JSmith01/zx-keyboard/delta/delta-c keyboard.jpg

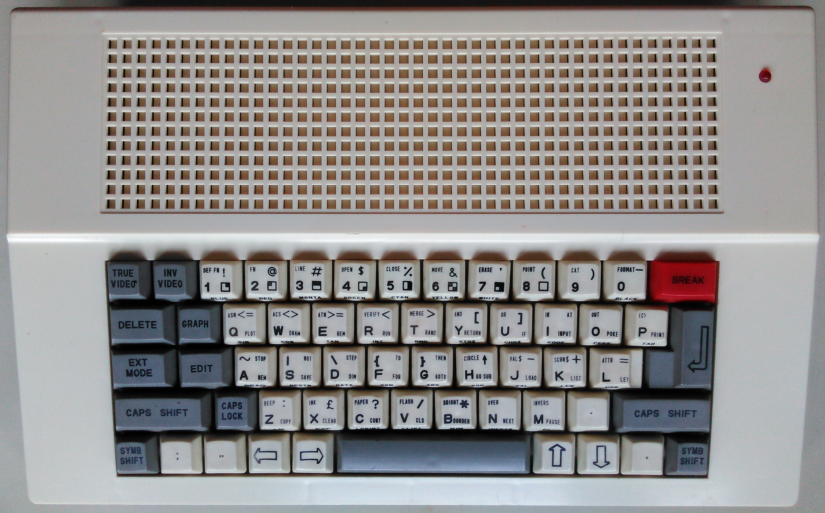
delta/delta-c keyboard.jpg
