JSmith01/zx-keyboard/keycap blueprints/key 1-1.jpg

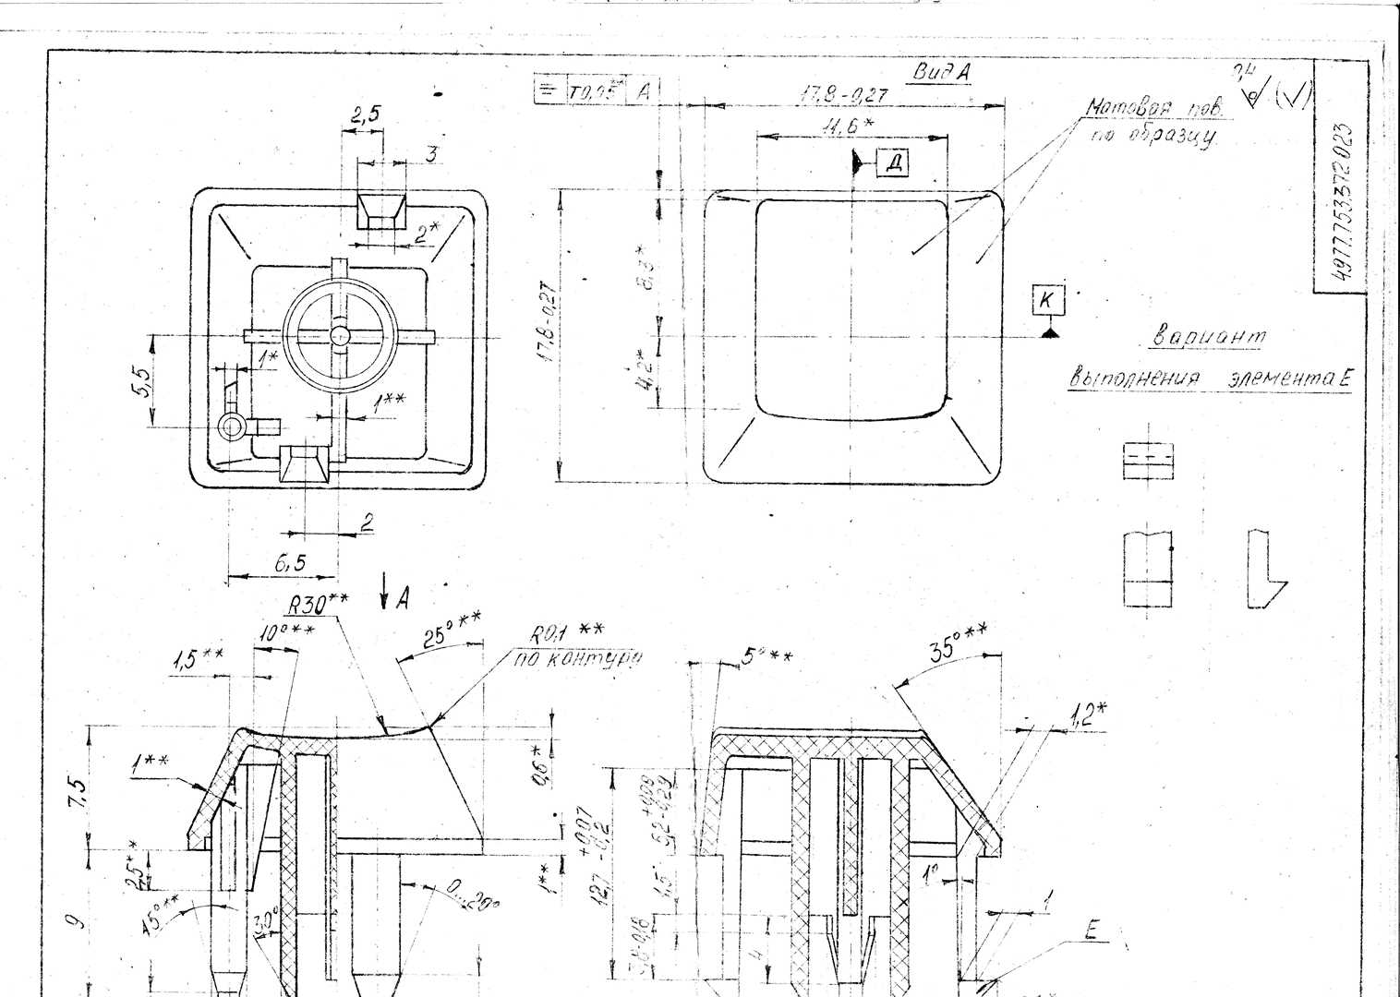
keycap blueprints/key 1-1.jpg
