JSmith01/zx-keyboard/keycap blueprints/key 2-1.jpg

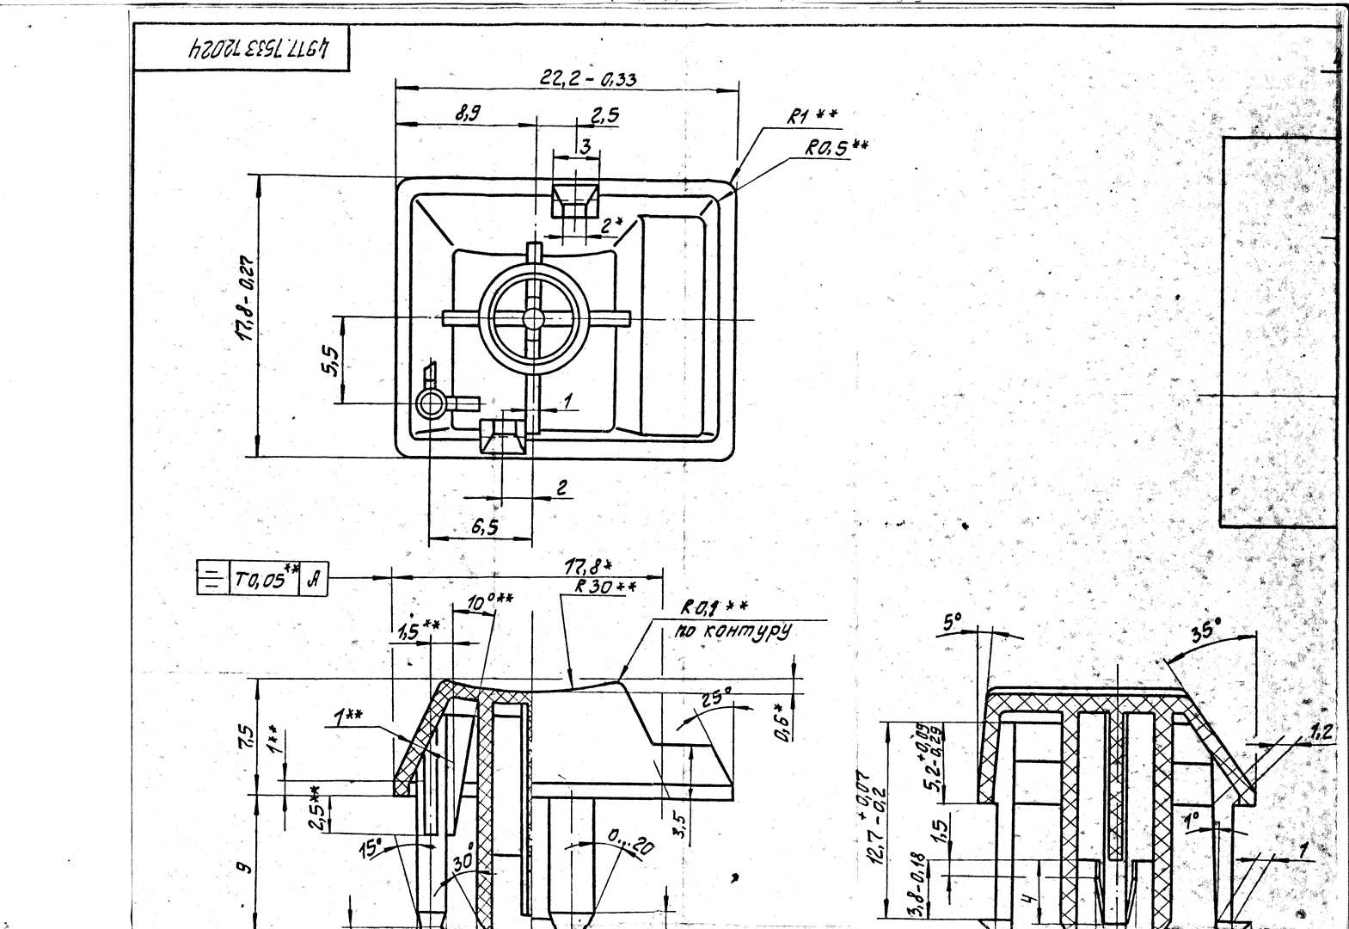
keycap blueprints/key 2-1.jpg
