JSmith01/zx-keyboard/keycap blueprints/key 2-2.jpg

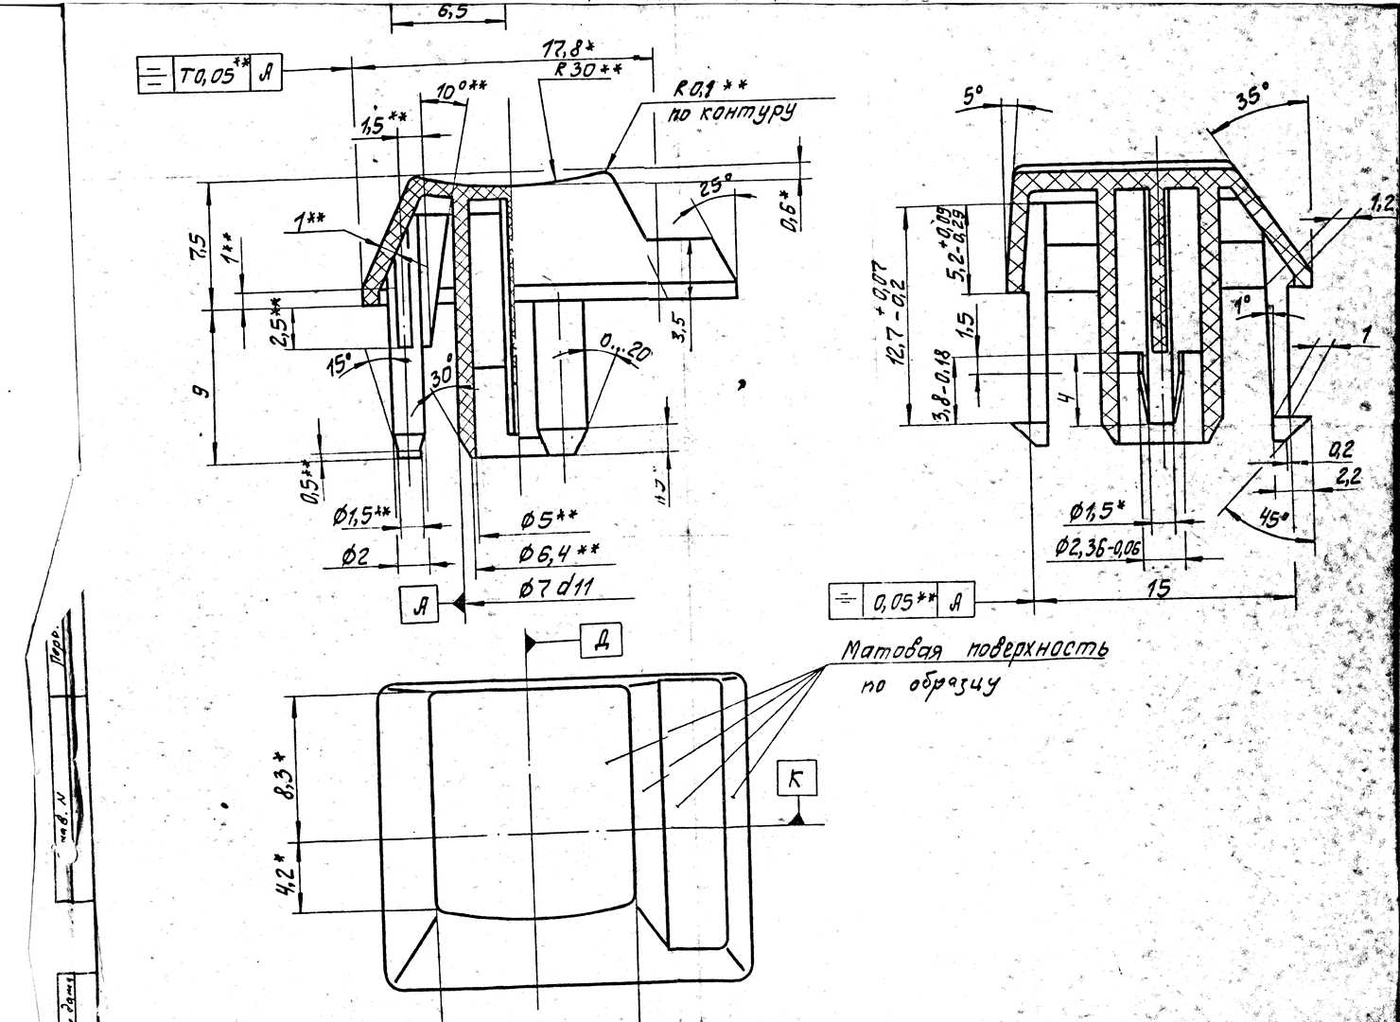
keycap blueprints/key 2-2.jpg
