JSmith01/zx-keyboard/keycap blueprints/key 2-3.jpg

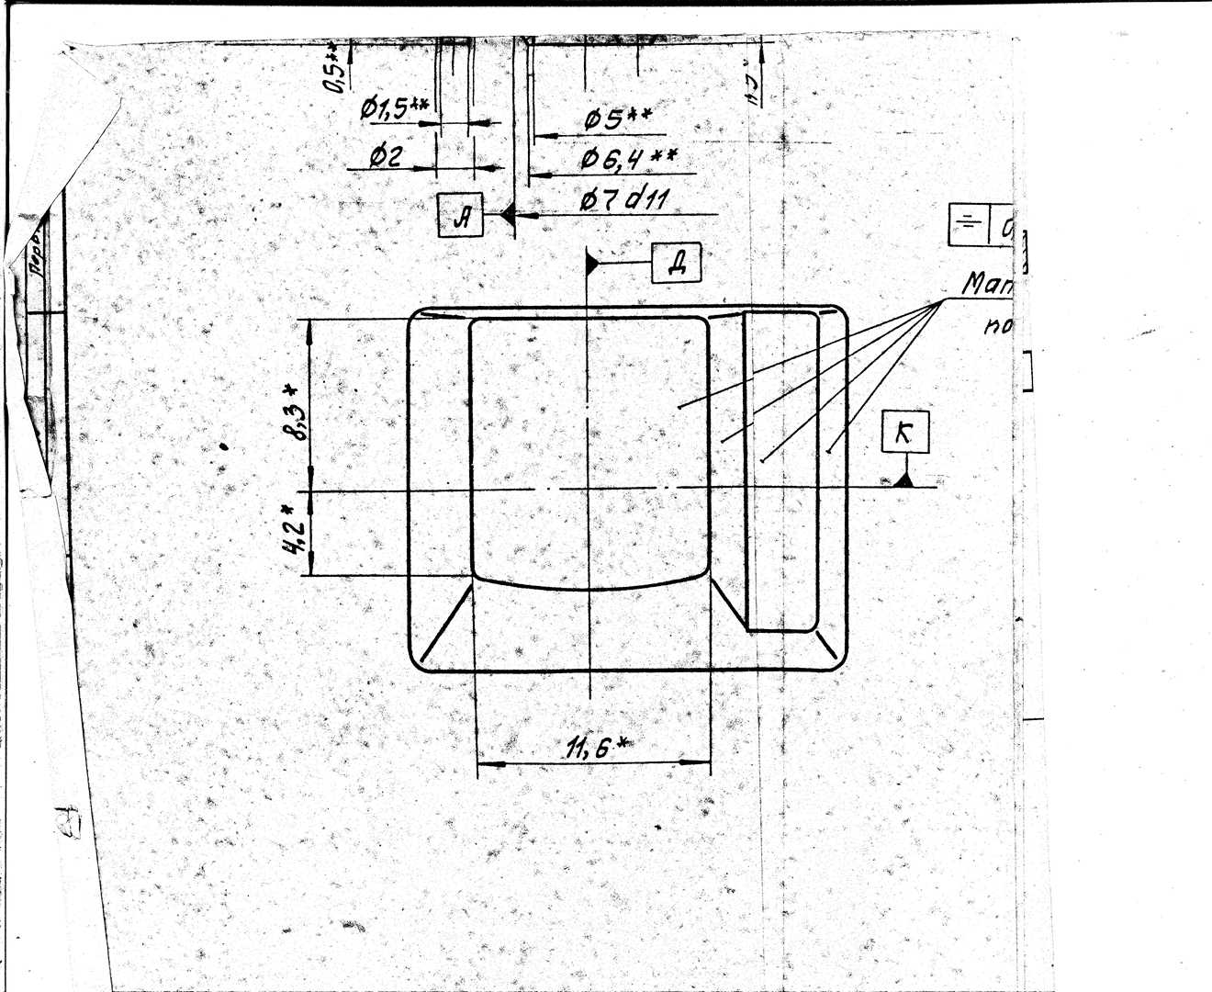
keycap blueprints/key 2-3.jpg
