JSmith01/zx-keyboard/keycap blueprints/key 3-1.jpg

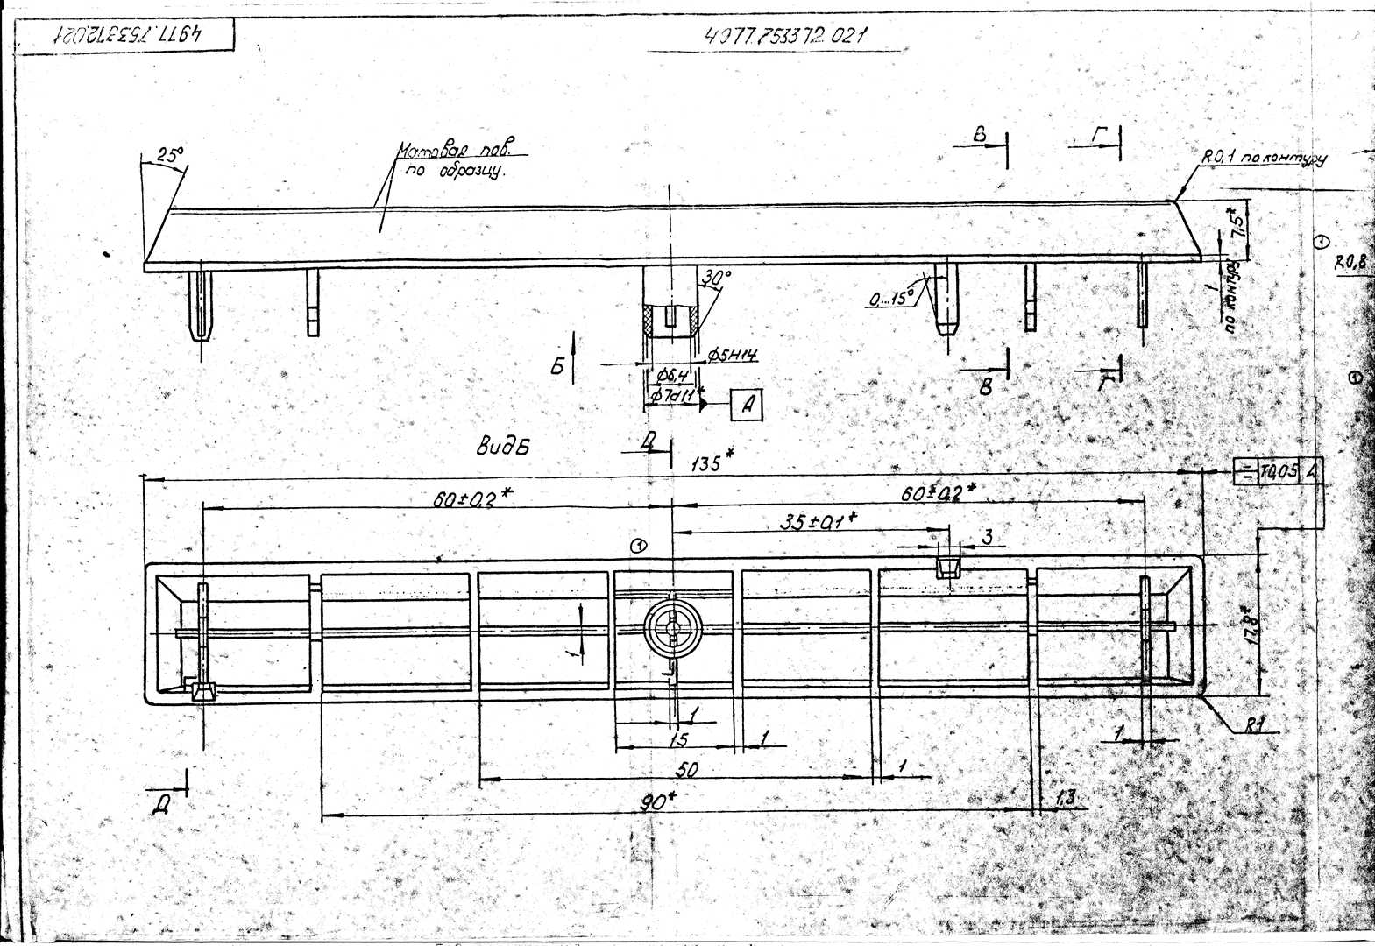
keycap blueprints/key 3-1.jpg
