JSmith01/zx-keyboard/keycap blueprints/key 3-2.jpg

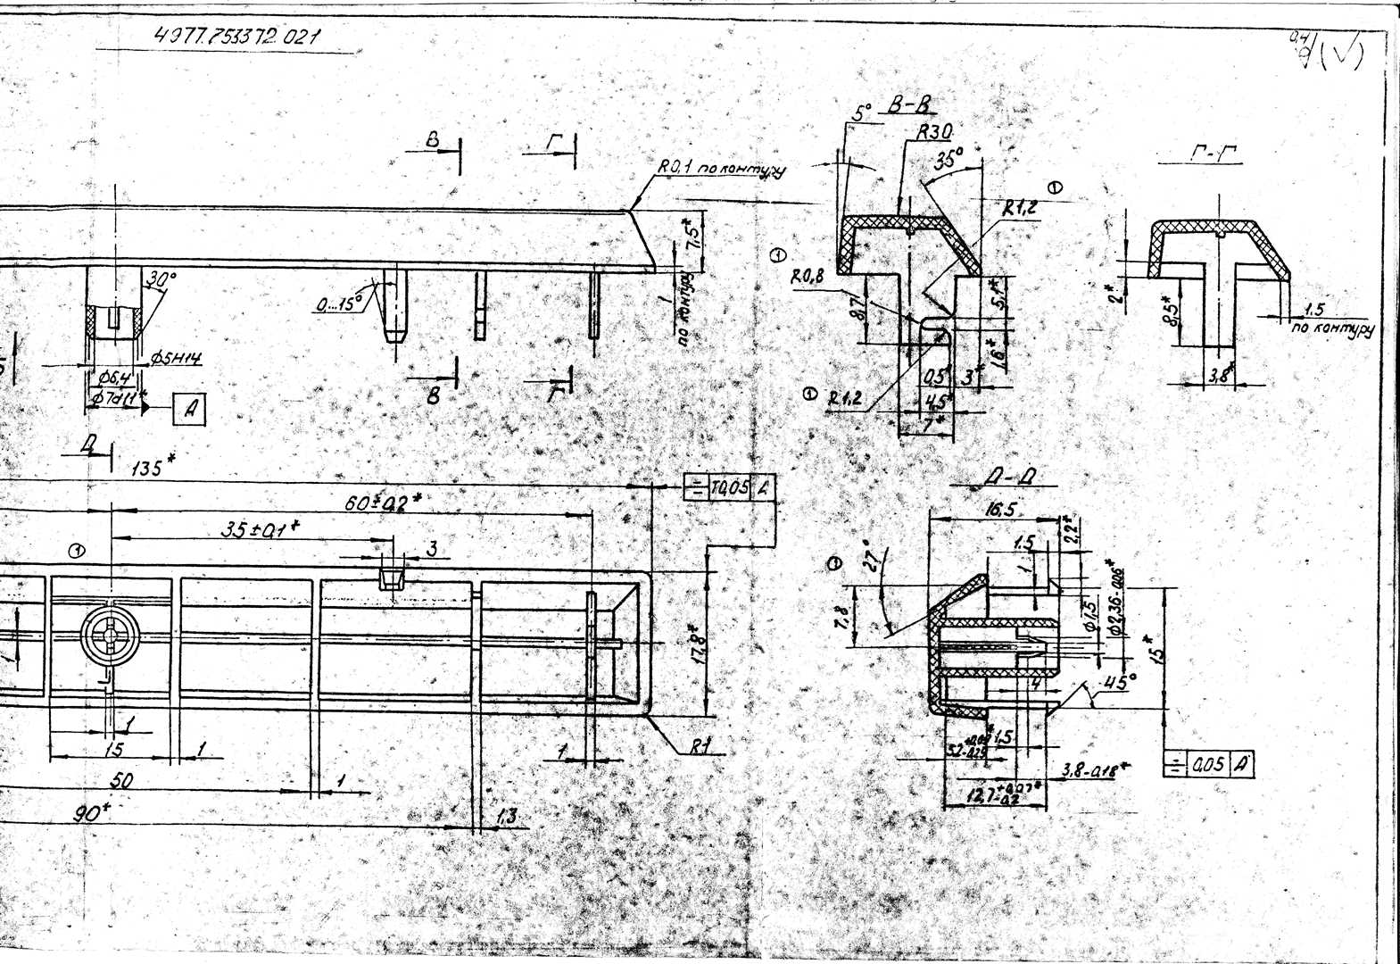
keycap blueprints/key 3-2.jpg
