JSmith01/zx-keyboard/keycap blueprints/key 4-1.jpg

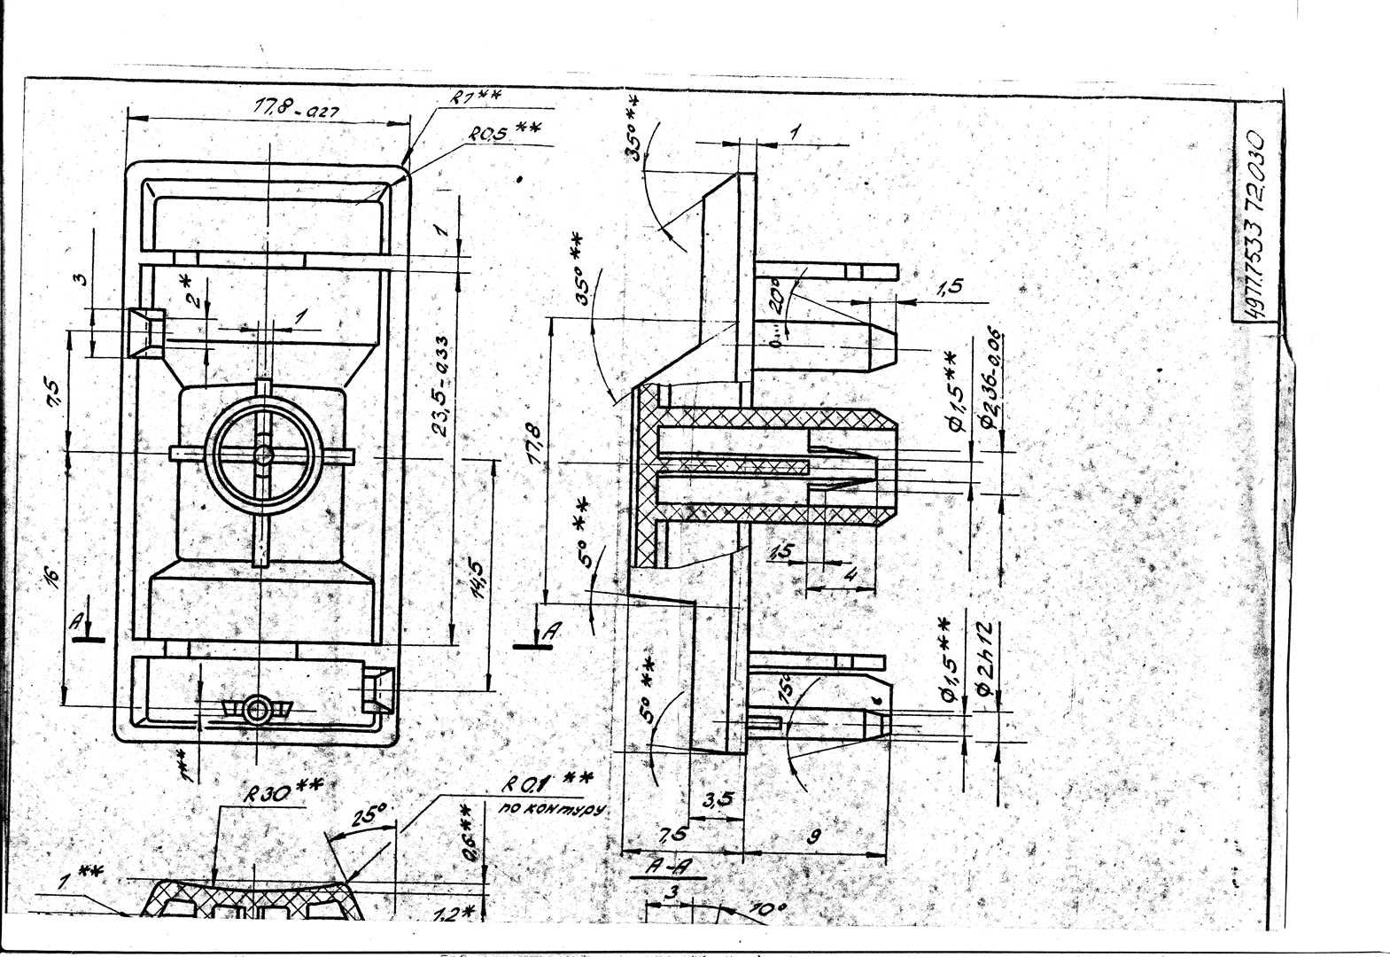
keycap blueprints/key 4-1.jpg
