JSmith01/zx-keyboard/keycap blueprints/key 4-2.jpg

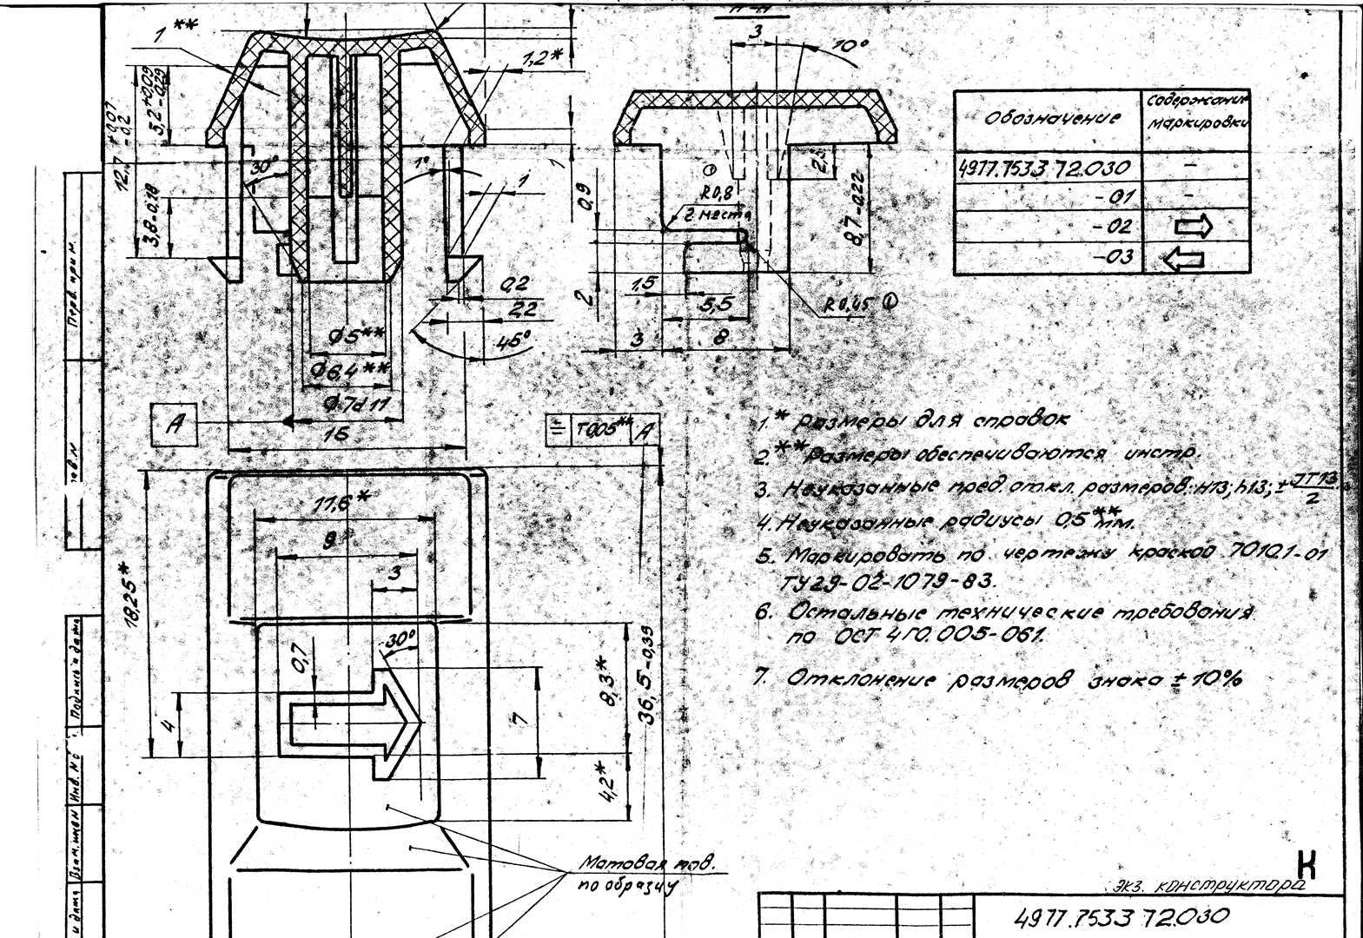
keycap blueprints/key 4-2.jpg
