JSmith01/zx-keyboard/keycap blueprints/key 4-3.jpg

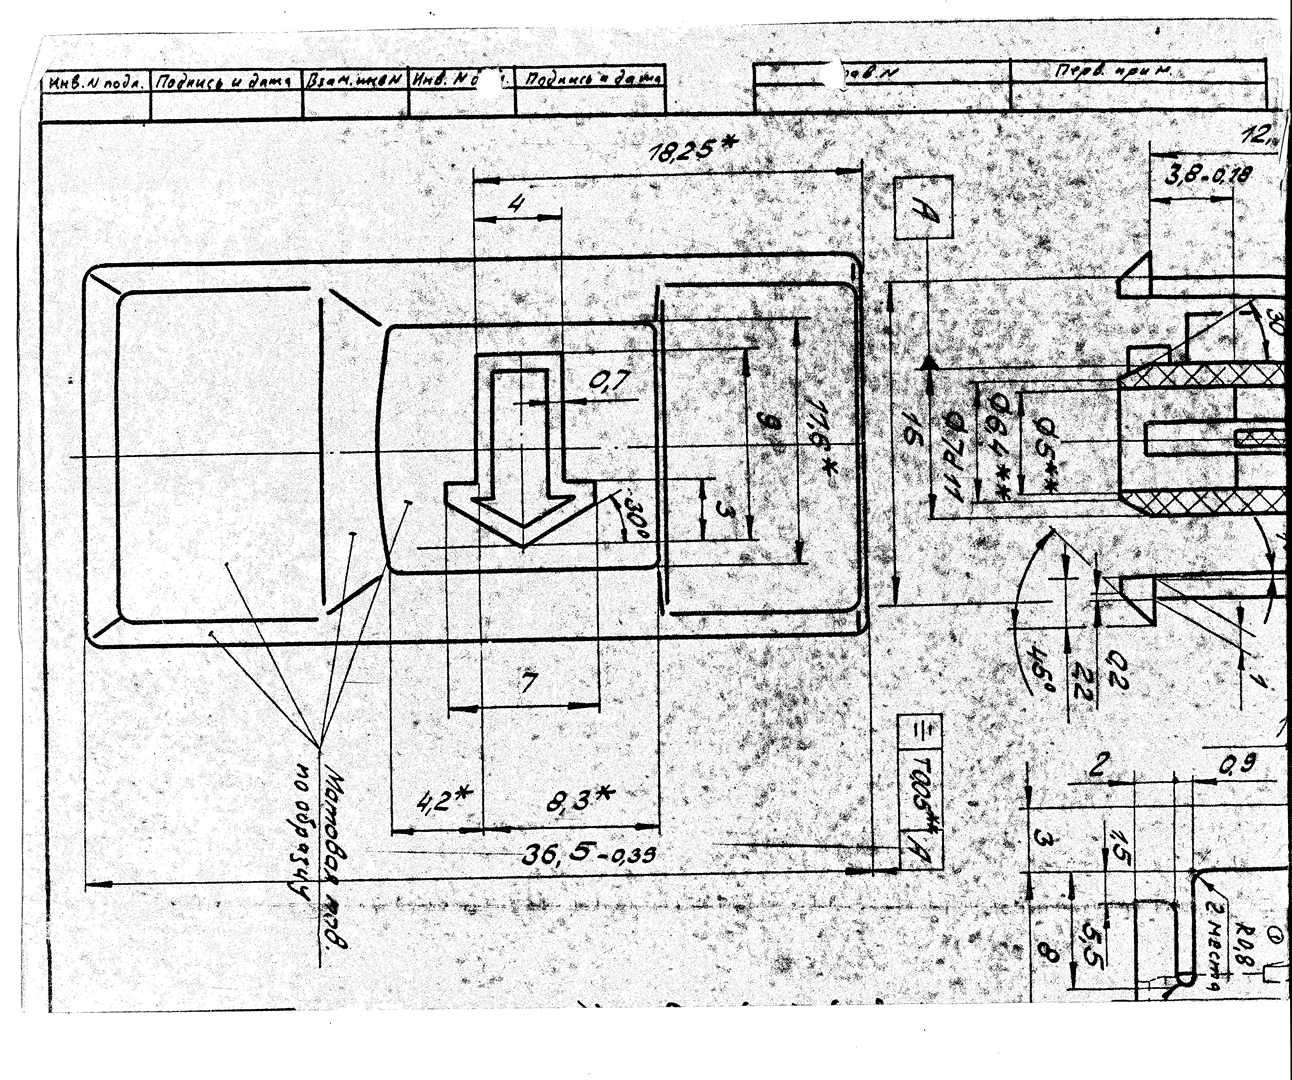
keycap blueprints/key 4-3.jpg
