JSmith01/zx-keyboard/keycap blueprints/key 5-2.jpg

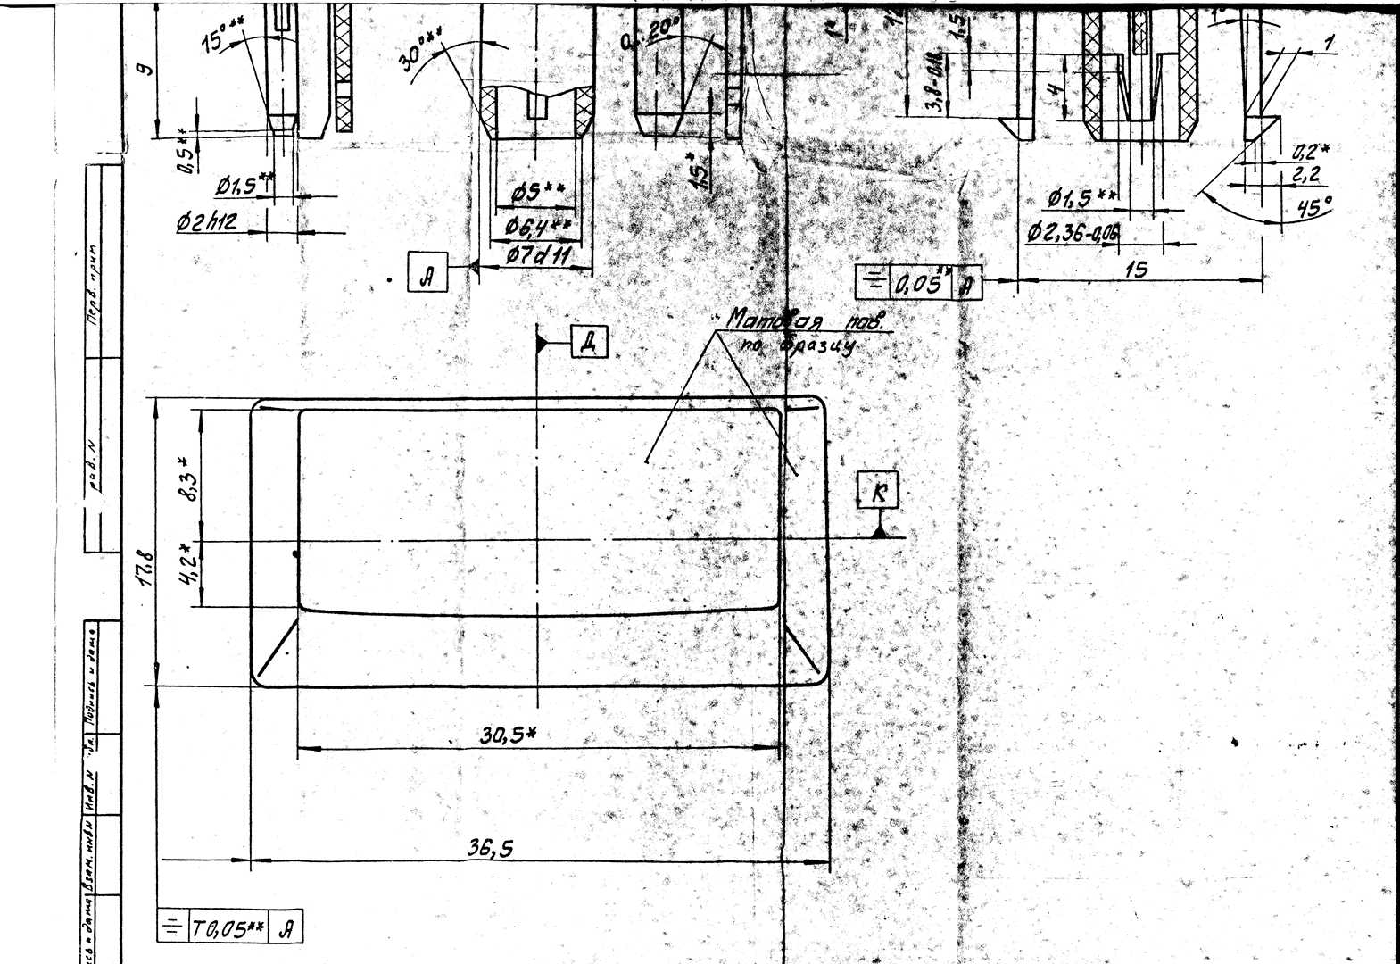
keycap blueprints/key 5-2.jpg
