JSmith01/zx-keyboard/keycap blueprints/key 6-2.jpg

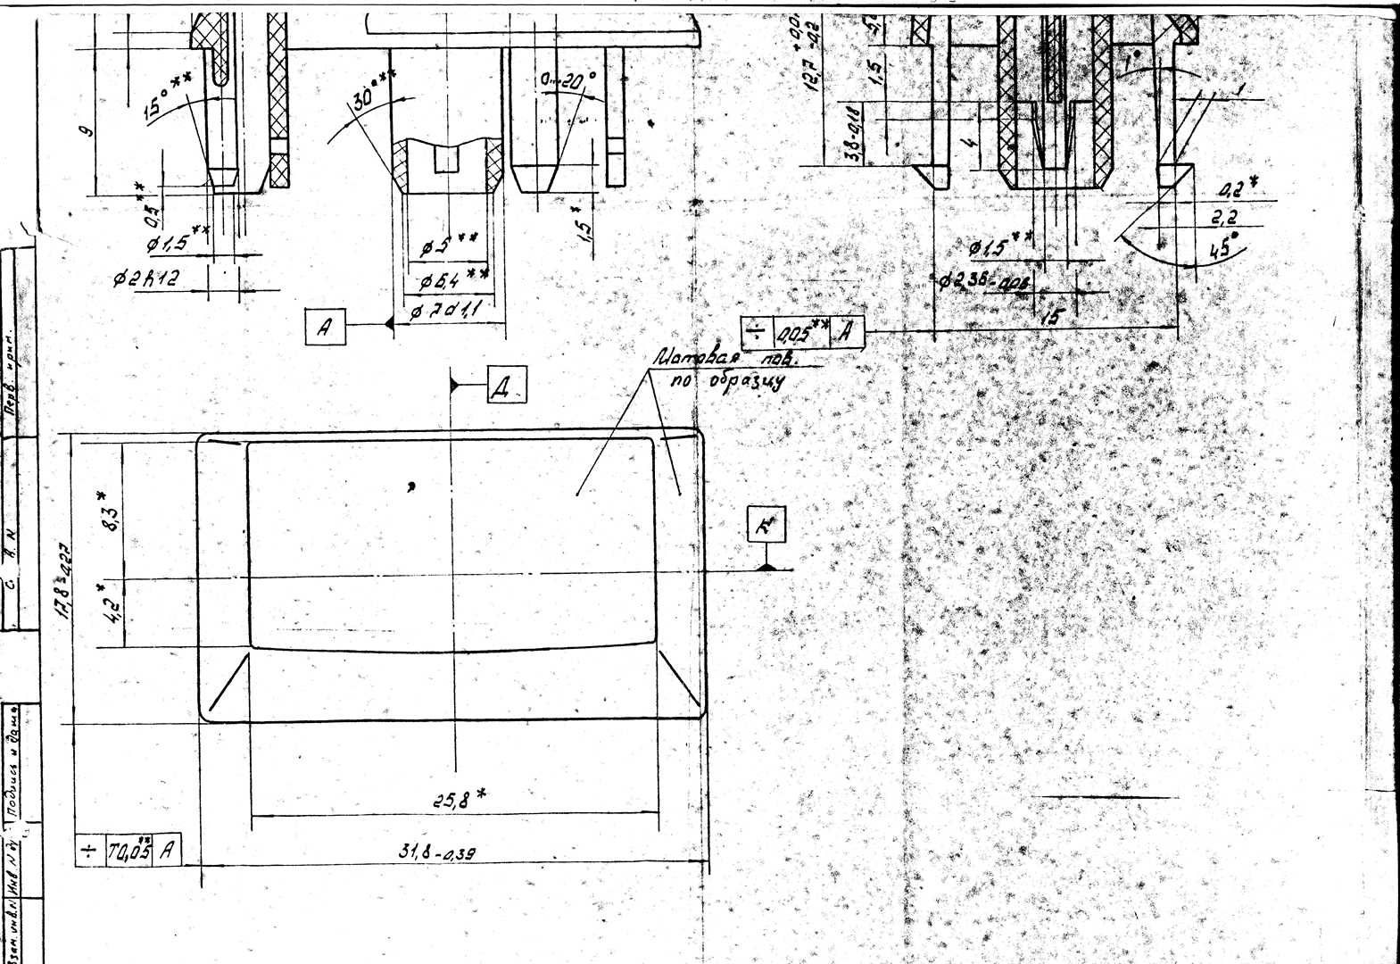
keycap blueprints/key 6-2.jpg
