JSmith01/zx-keyboard/keycap blueprints/key 7-1.jpg

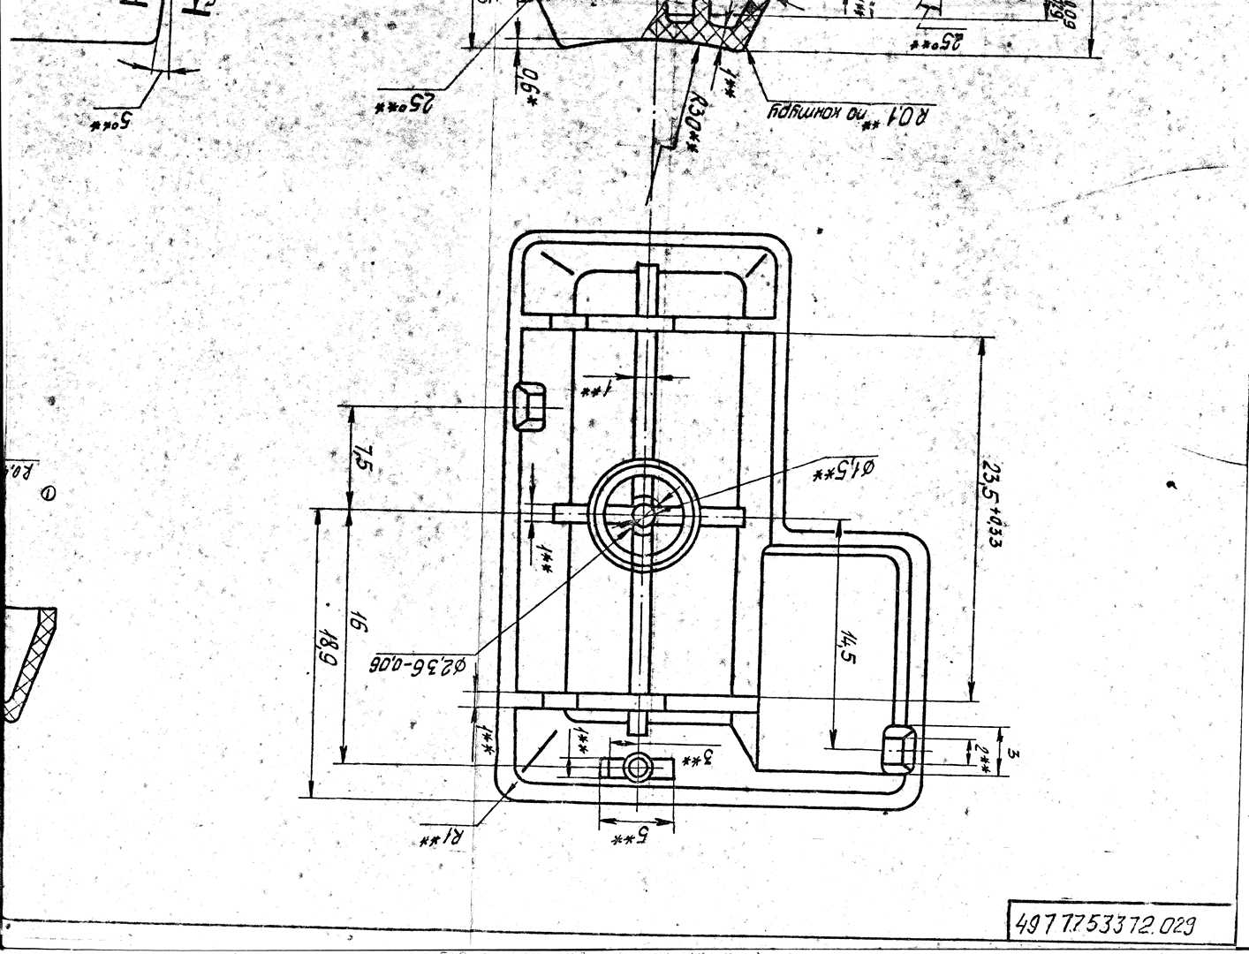
keycap blueprints/key 7-1.jpg
