JSmith01/zx-keyboard/keycap blueprints/key 7-2.jpg

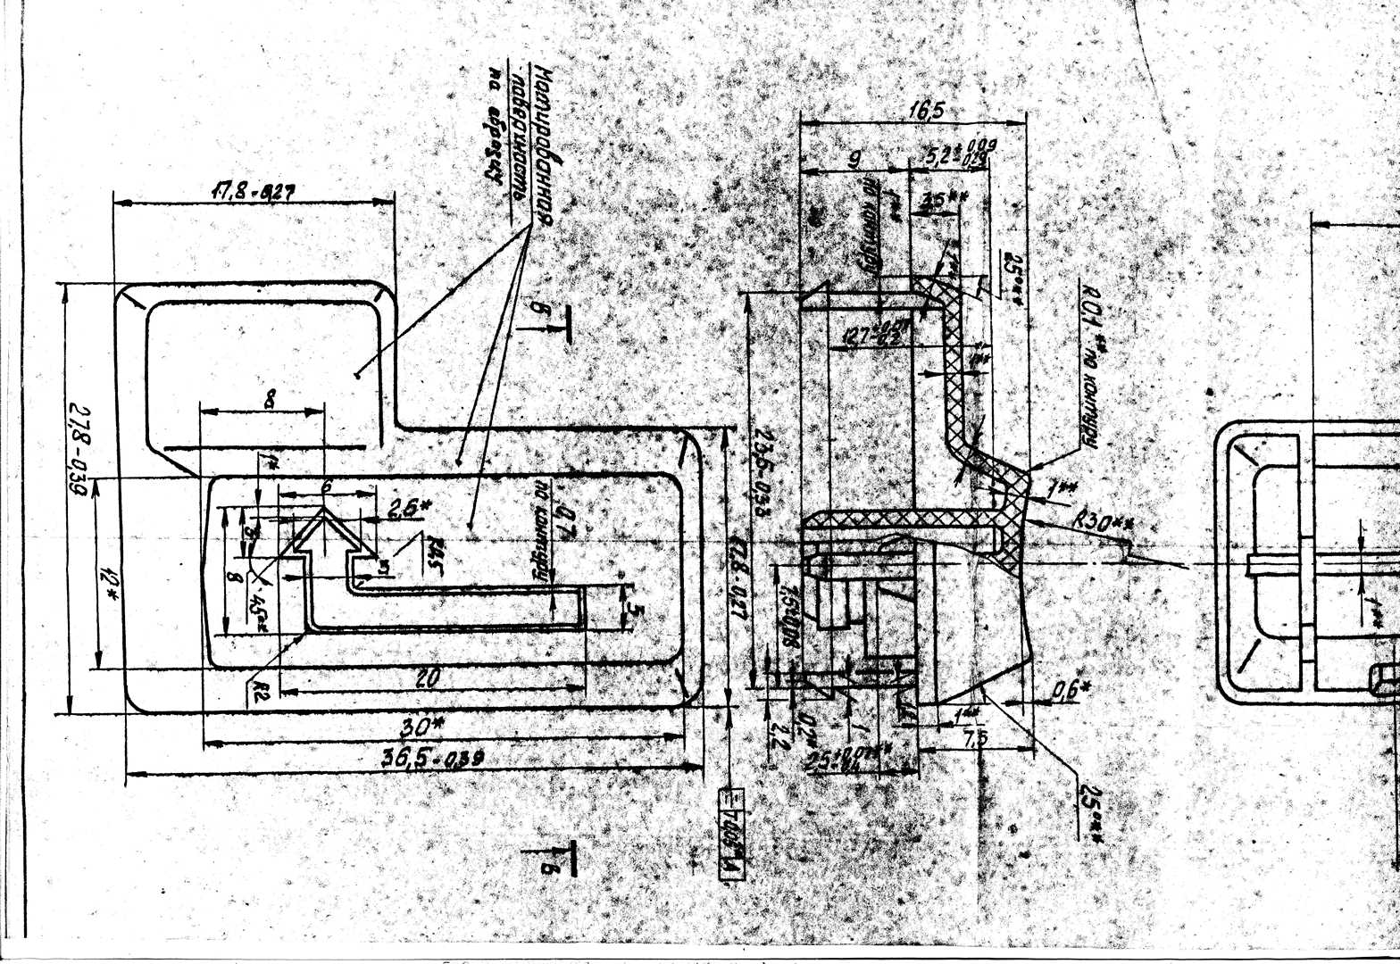
keycap blueprints/key 7-2.jpg
