JSmith01/zx-keyboard/keycap blueprints/key 7-3.jpg

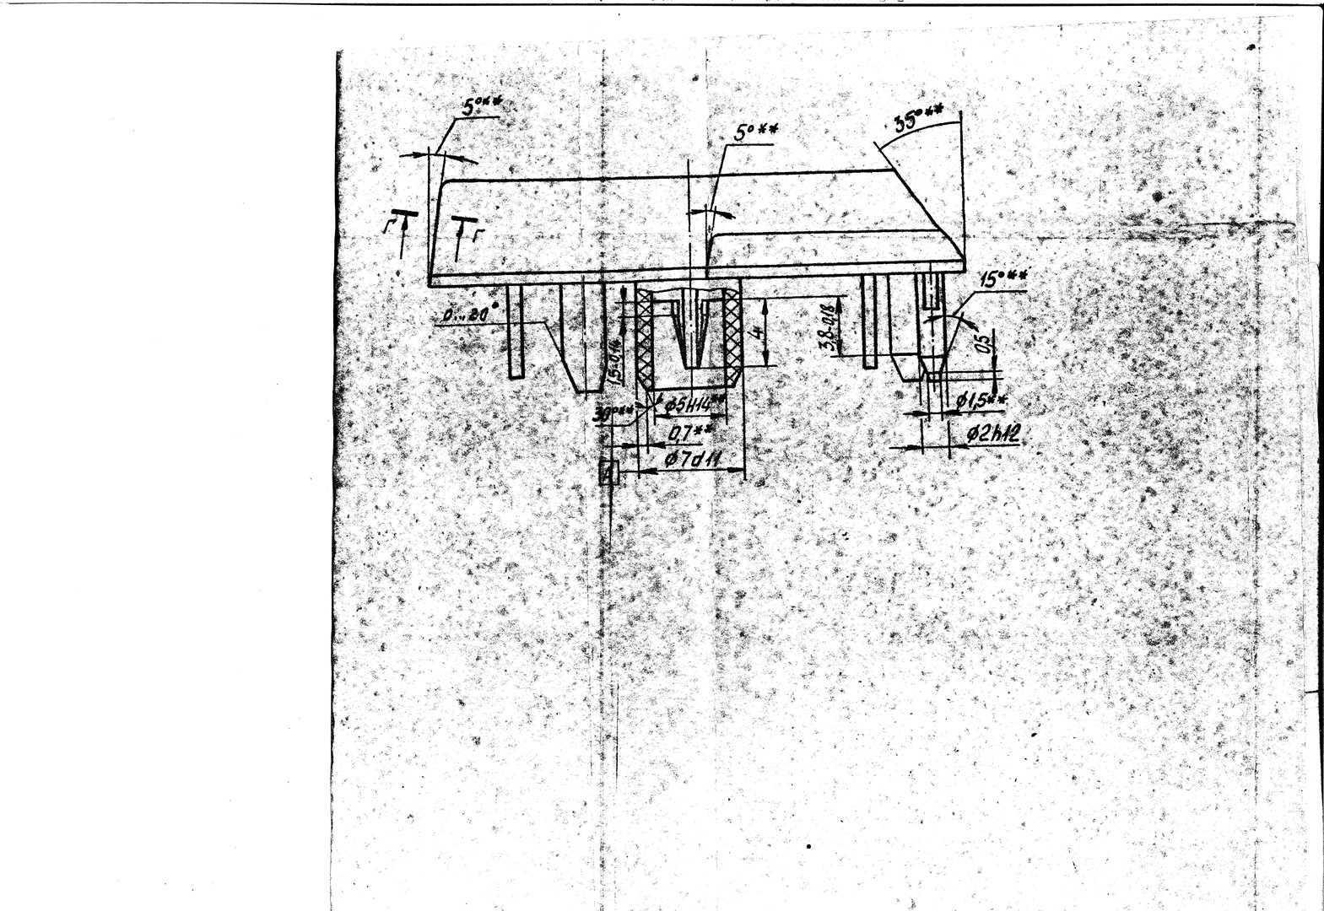
keycap blueprints/key 7-3.jpg
