JSmith01/zx-keyboard/keycap blueprints/key 7-4.jpg

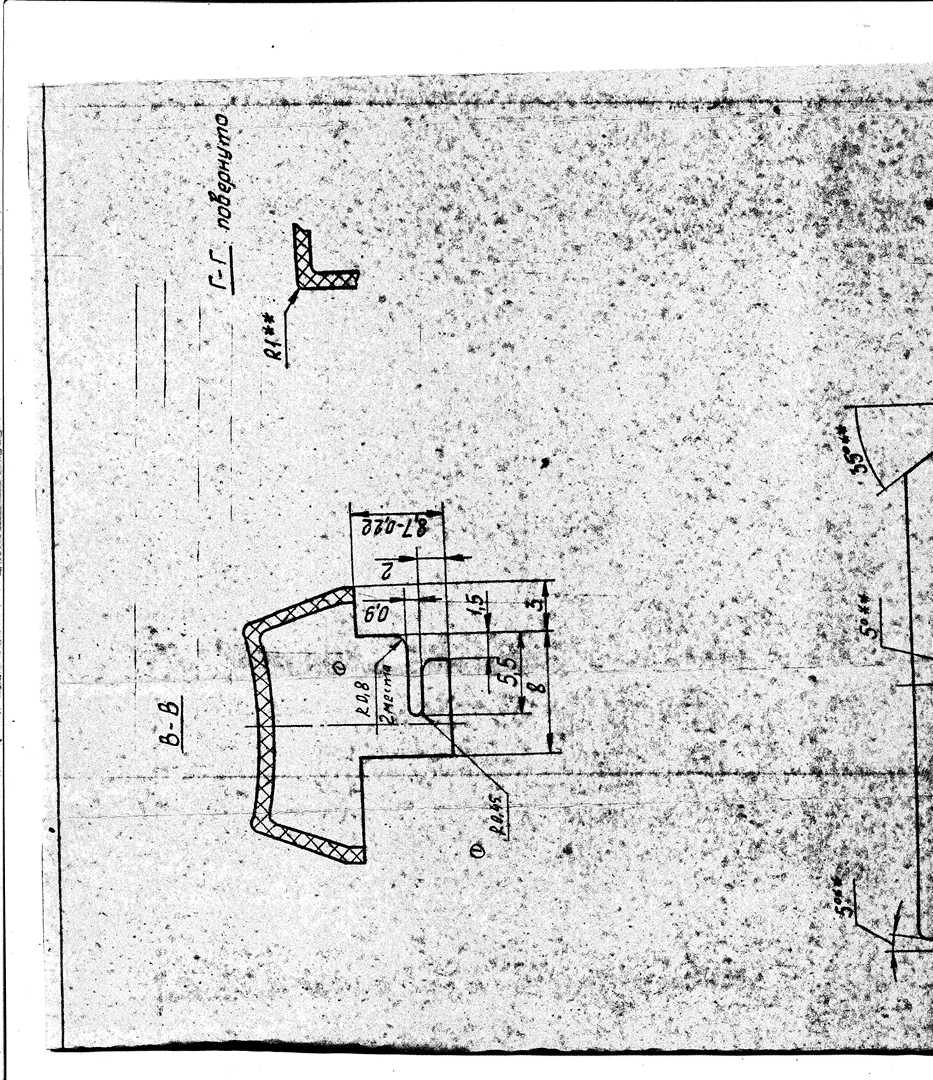
keycap blueprints/key 7-4.jpg
