JSmith01/zx-keyboard/pc-58-case/pictures/Image00006.jpg

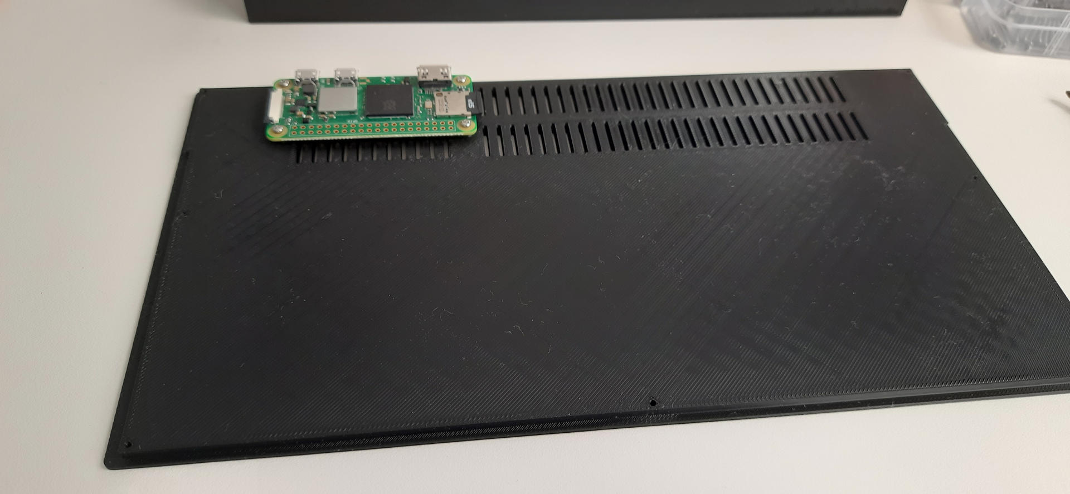
pc-58-case/pictures/Image00006.jpg
