JSmith01/zx-keyboard/pc-58-case/pictures/Image00007.jpg

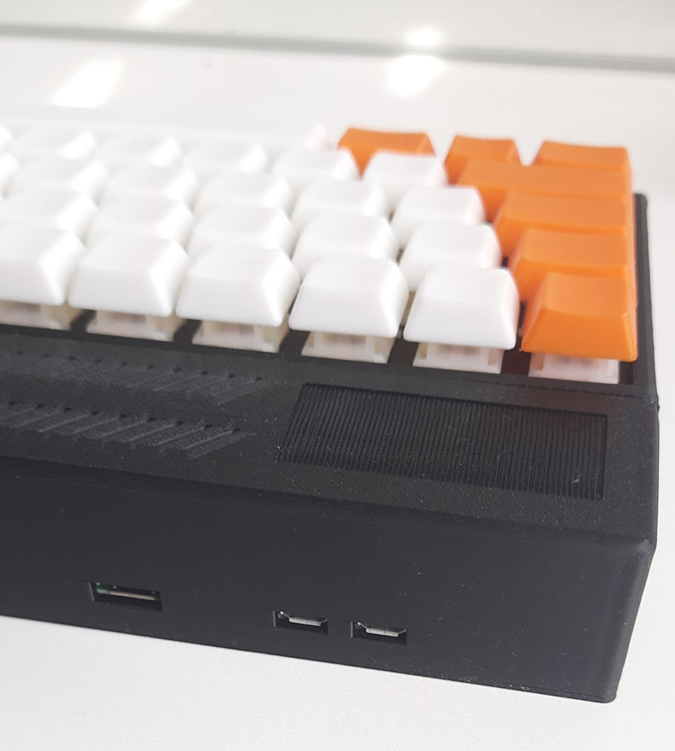
pc-58-case/pictures/Image00007.jpg
