JSmith01/zx-keyboard/pc-58-case/pictures/Image00008.jpg

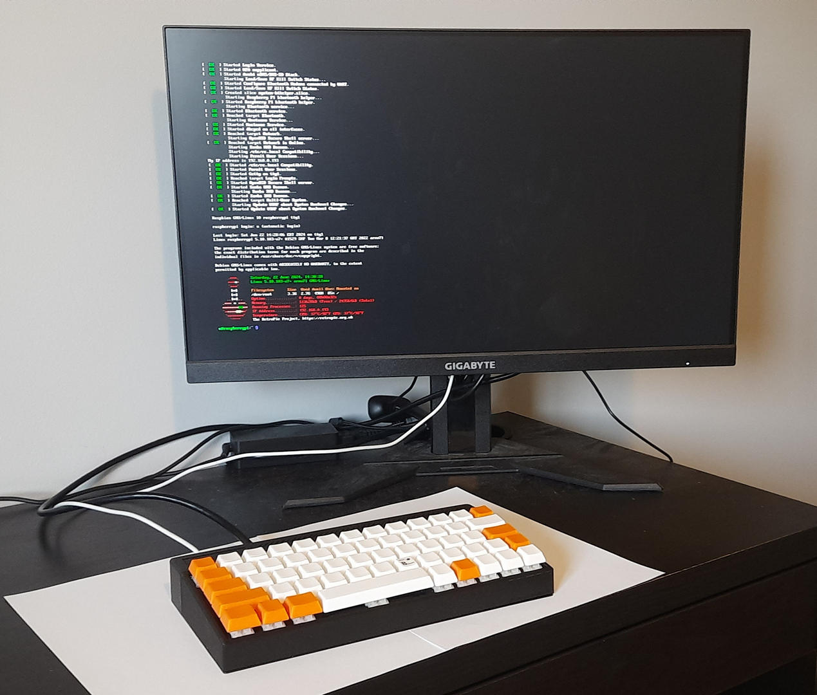
pc-58-case/pictures/Image00008.jpg
