JSmith01/zx-keyboard/test/test-plate.dxf

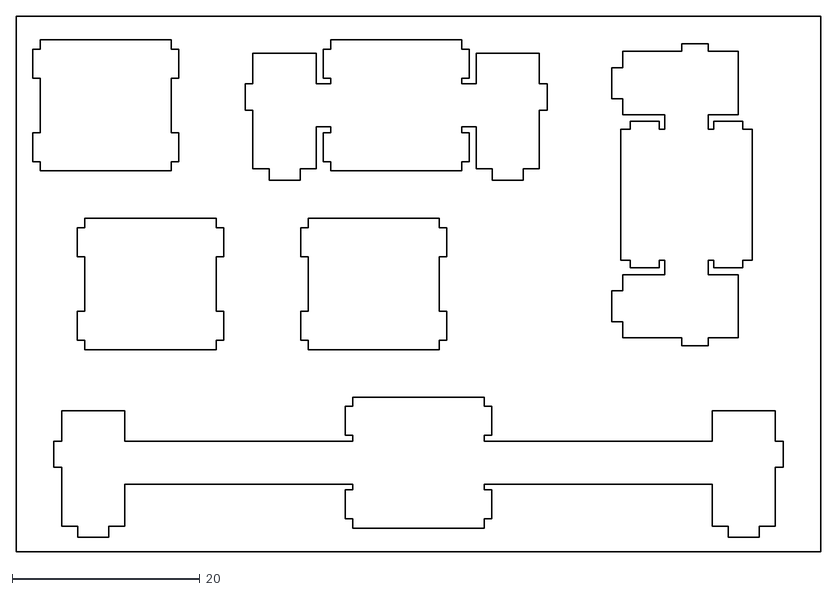
[picture p54: CAD file, 2024-06-14]
test/test-plate.dxf
85.7 x 57.1
