JSmith01/zx-keyboard/keycap models/1_25u stepped key.step

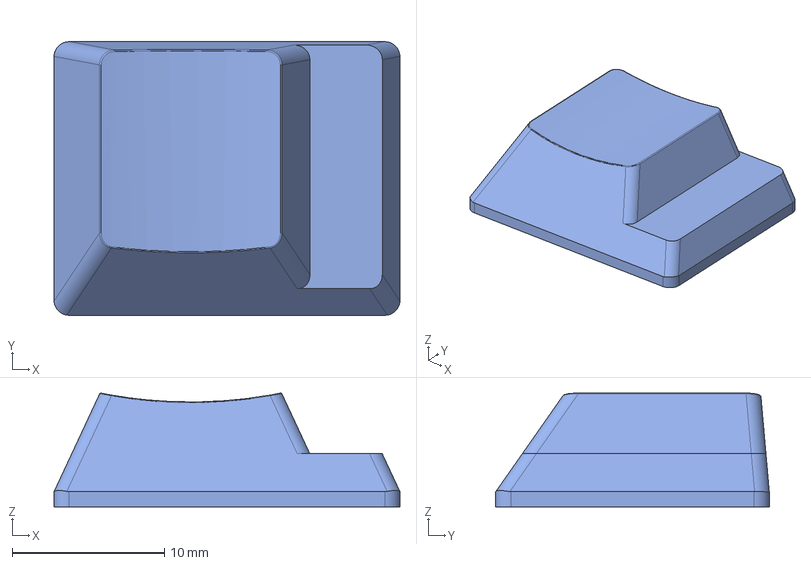
[picture p55: CAD file, 2024-06-16]
keycap models/1_25u stepped key.step
22.8 x 18.0 x 7.49 mm
