JSmith01/zx-keyboard/pc-58-case/back.step

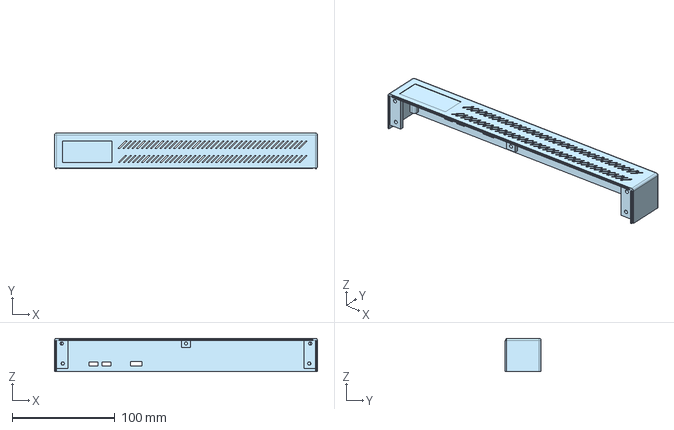
[picture p56: CAD file, 2024-09-09]
pc-58-case/back.step
256.0 x 35.3 x 32.6 mm
