JSmith01/zx-keyboard/pc-58-key/keycap-models/pc 2u key.step

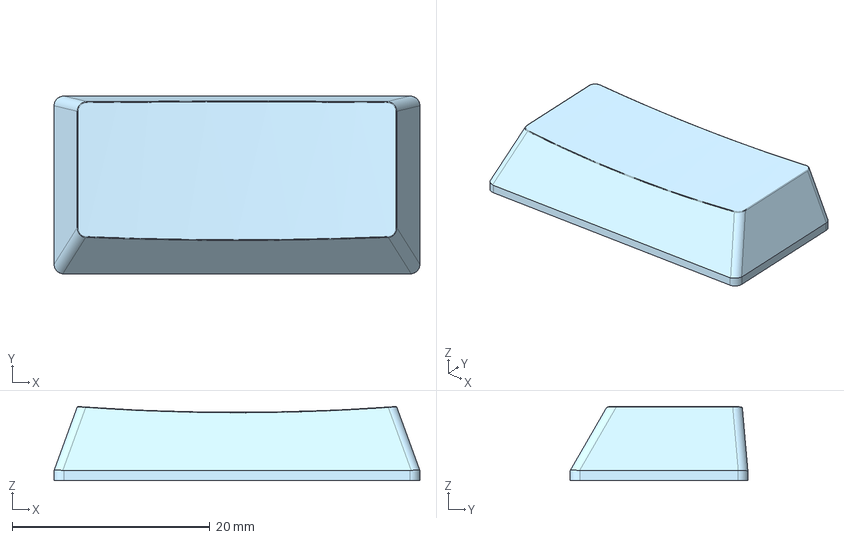
[picture p57: CAD file, 2024-09-09]
pc-58-key/keycap-models/pc 2u key.step
37.0 x 18.0 x 7.49 mm
