JSmith01/zx-keyboard/keycap models/1_5u key.step

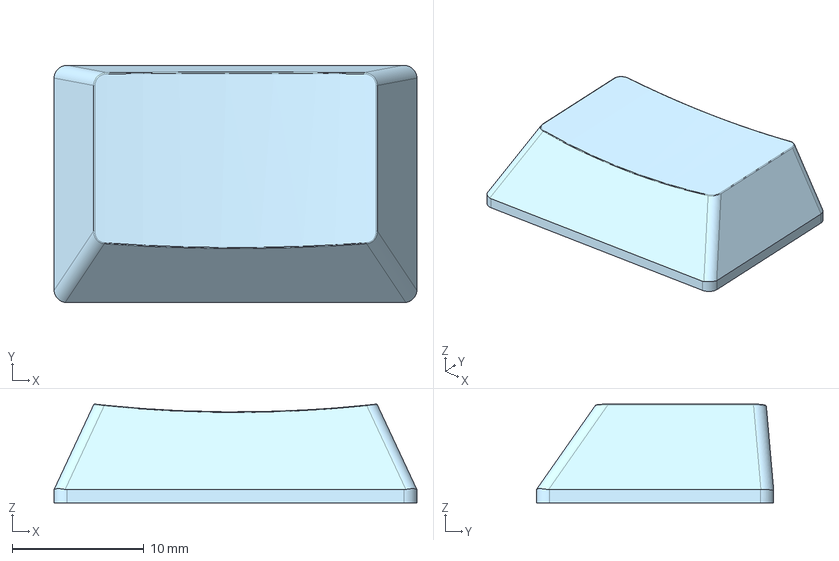
[picture p58: CAD file, 2024-06-16]
keycap models/1_5u key.step
27.5 x 18.0 x 7.49 mm
