JSmith01/zx-keyboard/pc-58-case/label.step

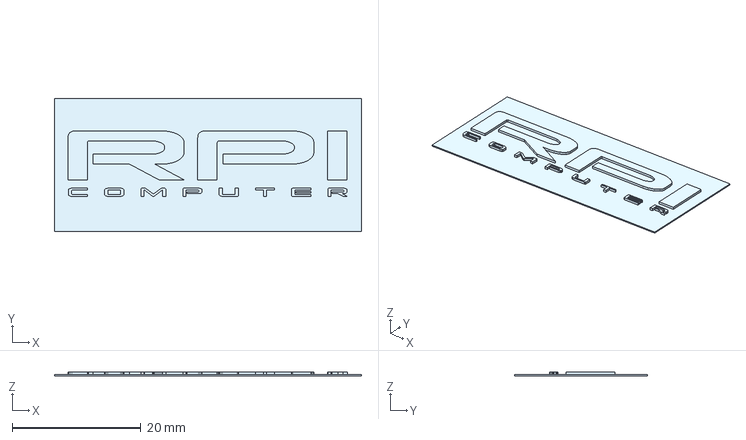
[picture p59: CAD file, 2024-09-09]
pc-58-case/label.step
47.6 x 20.6 x 0.6 mm
