JSmith01/zx-keyboard/pc-58-key/keycap-models/pc 1.5u key.step

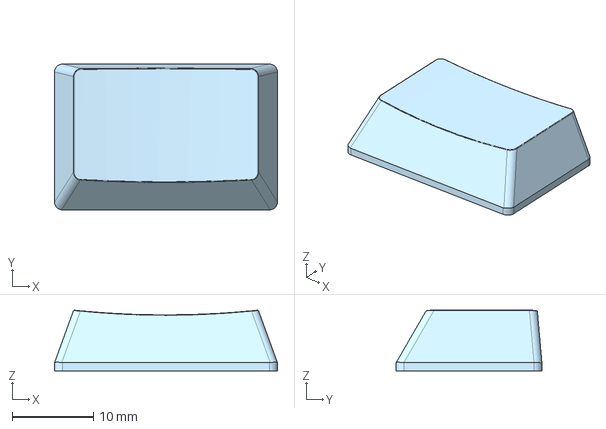
[picture p60: CAD file, 2024-09-09]
pc-58-key/keycap-models/pc 1.5u key.step
27.5 x 18.0 x 7.49 mm
