JSmith01/zx-keyboard/keycap models/2_25u key.step

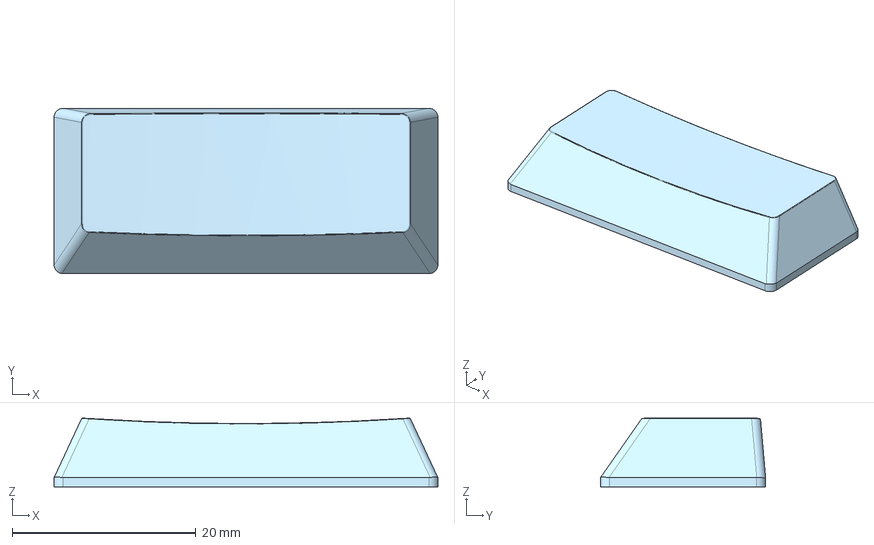
[picture p61: CAD file, 2024-06-16]
keycap models/2_25u key.step
41.8 x 18.0 x 7.50 mm
