JSmith01/zx-keyboard/pc-58-case/front.step

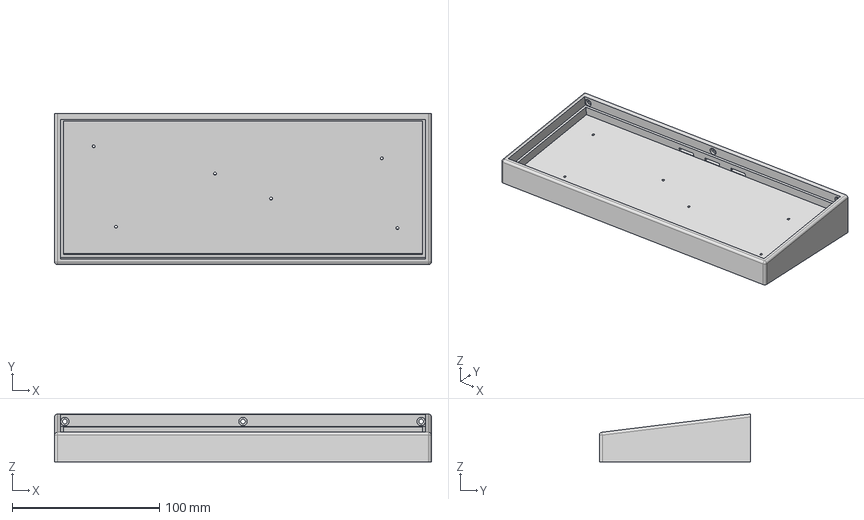
[picture p62: CAD file, 2024-09-09]
pc-58-case/front.step
256.0 x 102.7 x 32.6 mm
