JSmith01/zx-keyboard/pc-58-key/keycap-models/pc 1.25u key.step

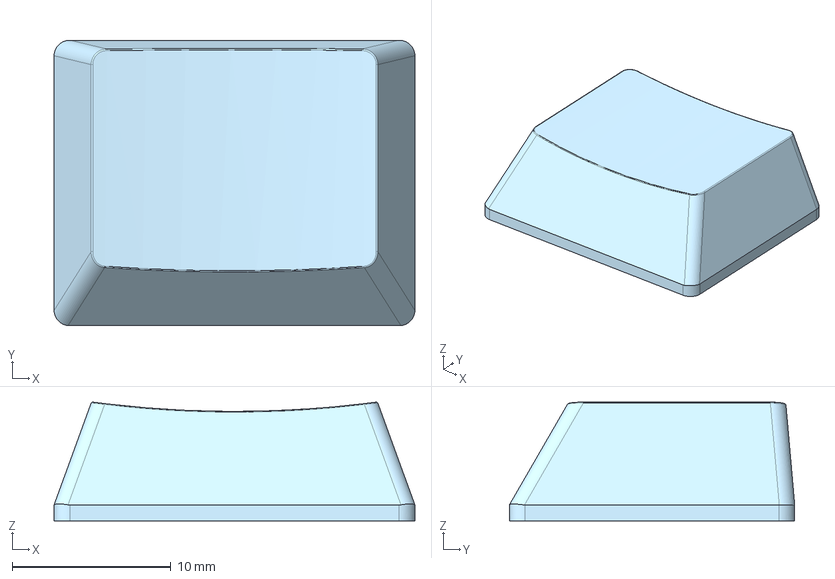
[picture p63: CAD file, 2024-09-09]
pc-58-key/keycap-models/pc 1.25u key.step
22.8 x 18.0 x 7.49 mm
