JSmith01/zx-keyboard/pc-58-case/plate.step

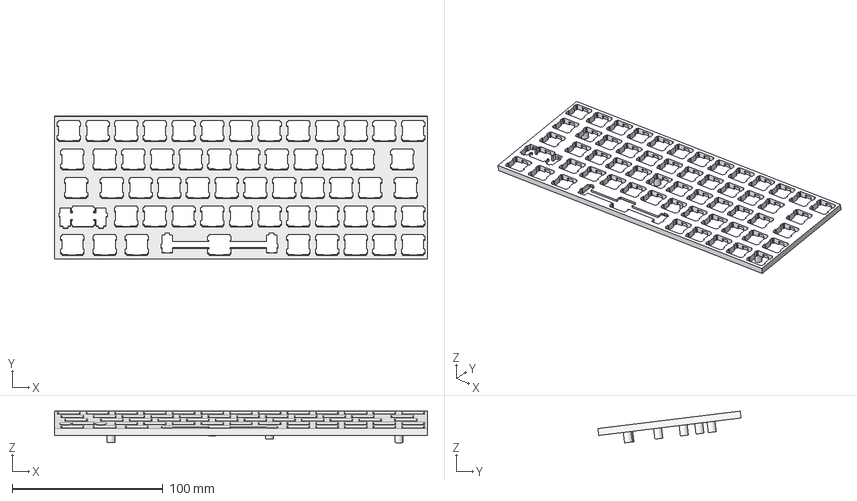
[picture p64: CAD file, 2024-09-09]
pc-58-case/plate.step
247.6 x 95.1 x 21.1 mm
