JSmith01/zx-keyboard/pc-58-key/keycap-models/pc 4.5u key.step

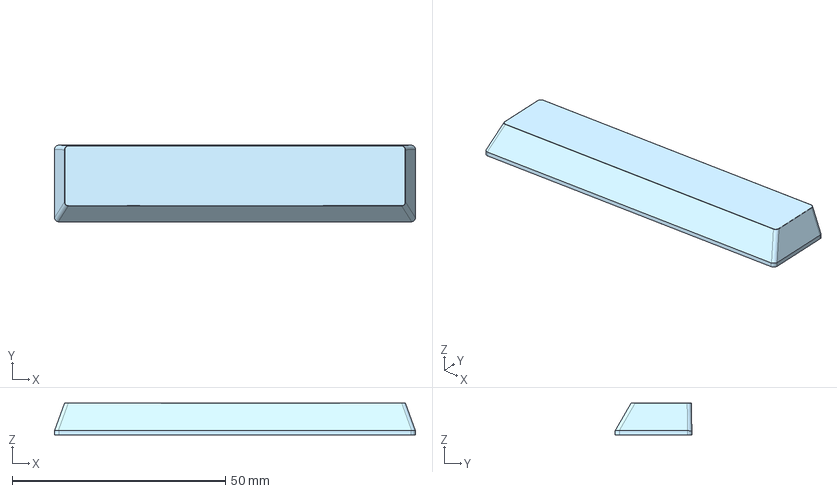
[picture p65: CAD file, 2024-09-09]
pc-58-key/keycap-models/pc 4.5u key.step
84.7 x 18.0 x 7.50 mm
