JSmith01/zx-keyboard/keycap models/6_25u key.step

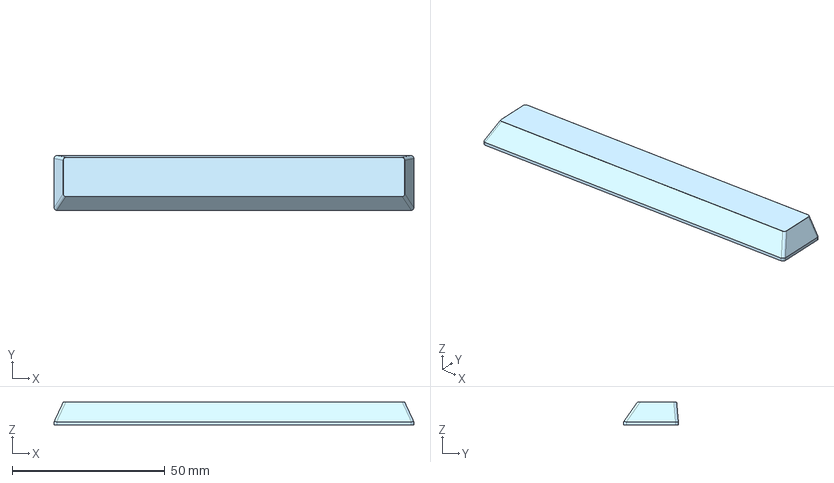
[picture p66: CAD file, 2024-06-16]
keycap models/6_25u key.step
118.0 x 18.0 x 7.50 mm
