JSmith01/zx-keyboard/keycap models/1_75u key.step

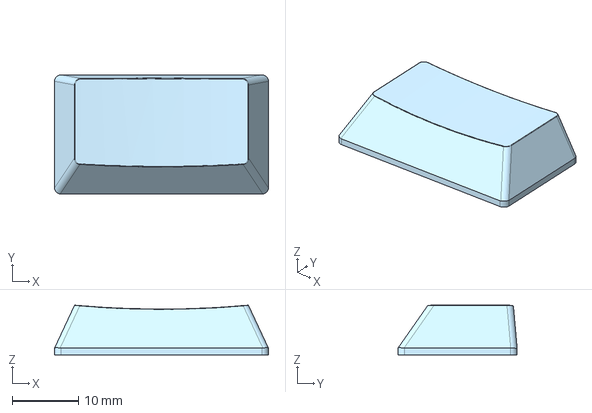
[picture p67: CAD file, 2024-06-16]
keycap models/1_75u key.step
32.3 x 18.0 x 7.49 mm
