JSmith01/zx-keyboard/keycap models/2u Enter.step

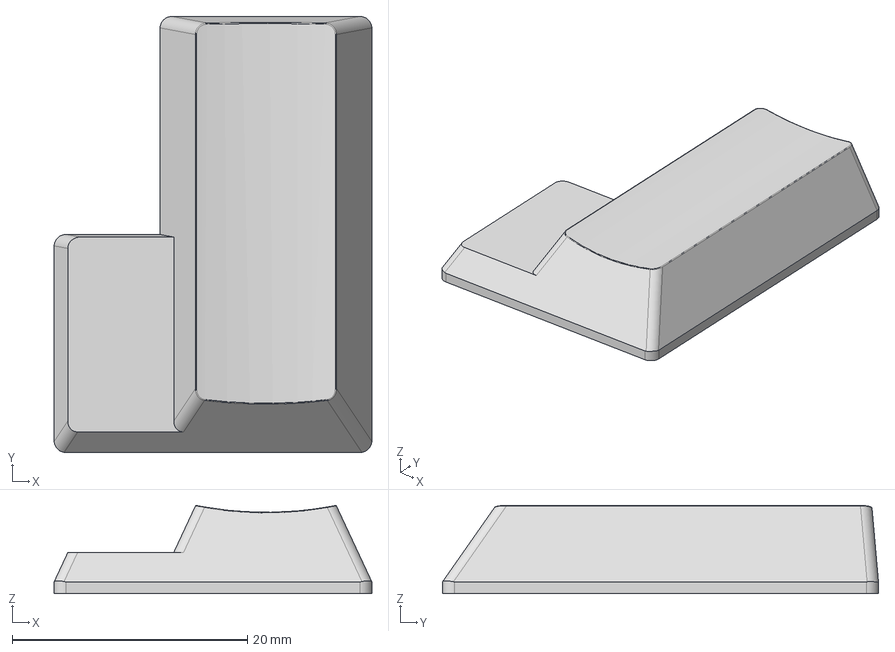
[picture p68: CAD file, 2024-06-16]
keycap models/2u Enter.step
27.0 x 37.1 x 7.49 mm
