JSmith01/zx-keyboard/keycap models/1u key.step

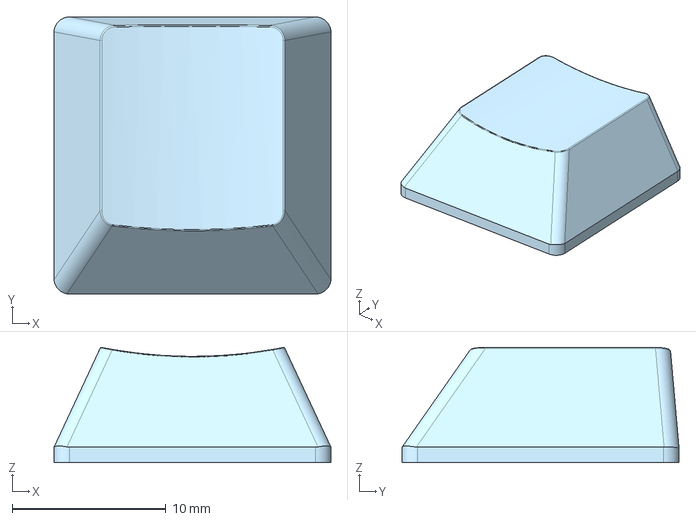
[picture p69: CAD file, 2024-06-16]
keycap models/1u key.step
18.0 x 18.0 x 7.49 mm
